MakeMagazinDE/Vendinator/Arduino Sketche/Komponenten-Tests/I2C_LCD_Hello_World/I2C_LCD_Hello_World/I2C_LCD_Hello_World.ino

//YWROBOT
//Compatible with the Arduino IDE 1.0
//Library version:1.1
#include <Wire.h> 
#include <LiquidCrystal_I2C.h>

LiquidCrystal_I2C lcd(0x27,20,4);  // set the LCD address to 0x27 for a 16 chars and 2 line display

void setup()
{
  lcd.init();                      // initialize the lcd 
  lcd.init();
  // Print a message to the LCD.
  lcd.backlight();
  lcd.setCursor(3,0);
  lcd.print("Hello, world!");
  lcd.setCursor(0,1);
  lcd.print("Zeile 2");
   lcd.setCursor(0,2);
  lcd.print("Zeile 3");
   lcd.setCursor(0,3);
  lcd.print("Zeile 4");
}


void loop()
{
}
